mlab-modules/BLE03/doc/gen/dxf/BLE03-B_Cu.dxf

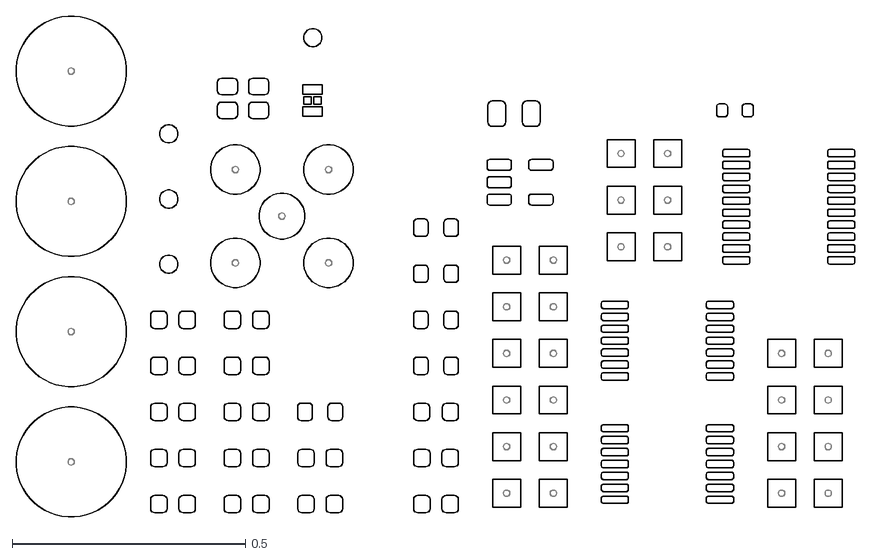
[picture p10: CAD file, 2026-02-14]
doc/gen/dxf/BLE03-B_Cu.dxf
1.80 x 1.07
